airpocket-soundman/egg-analyzer/img/DSC_0775_.jpg

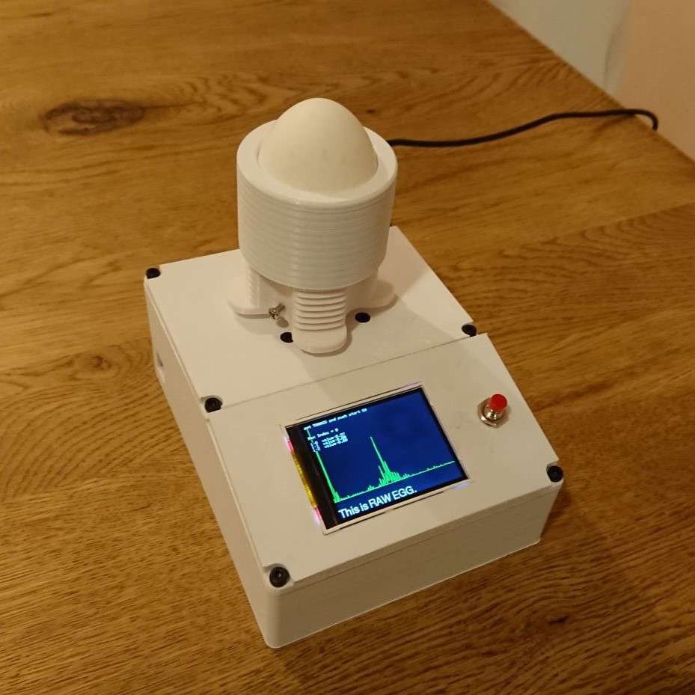
img/DSC_0775_.jpg
