airpocket-soundman/egg-analyzer/img/DSC_0773_.jpg

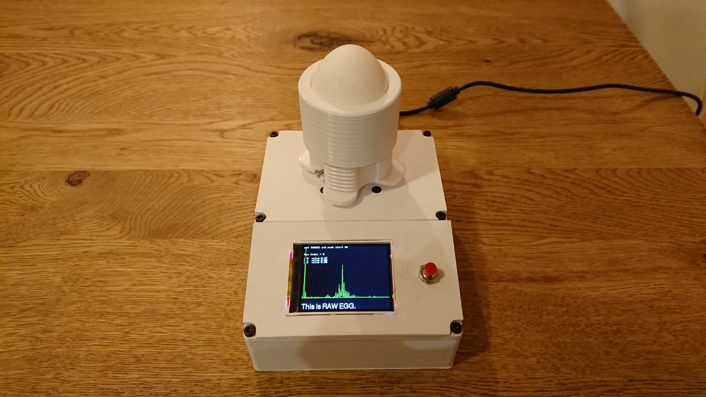
img/DSC_0773_.jpg
