airpocket-soundman/egg-analyzer/img/DSC_0776_.jpg

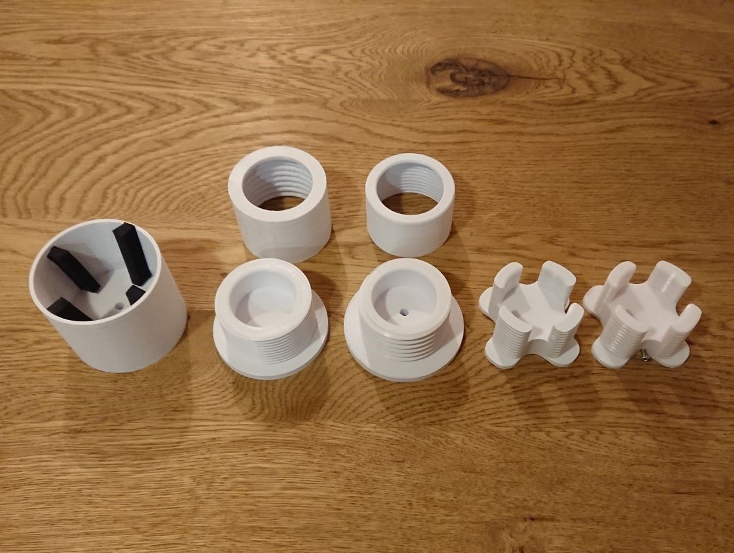
img/DSC_0776_.jpg
