airpocket-soundman/egg-analyzer/img/DSC_0781_.jpg

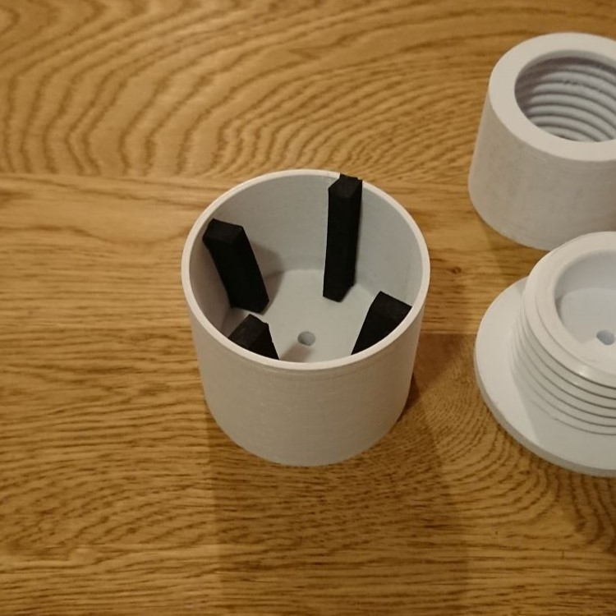
img/DSC_0781_.jpg
