airpocket-soundman/egg-analyzer/img/DSC_0782_.jpg

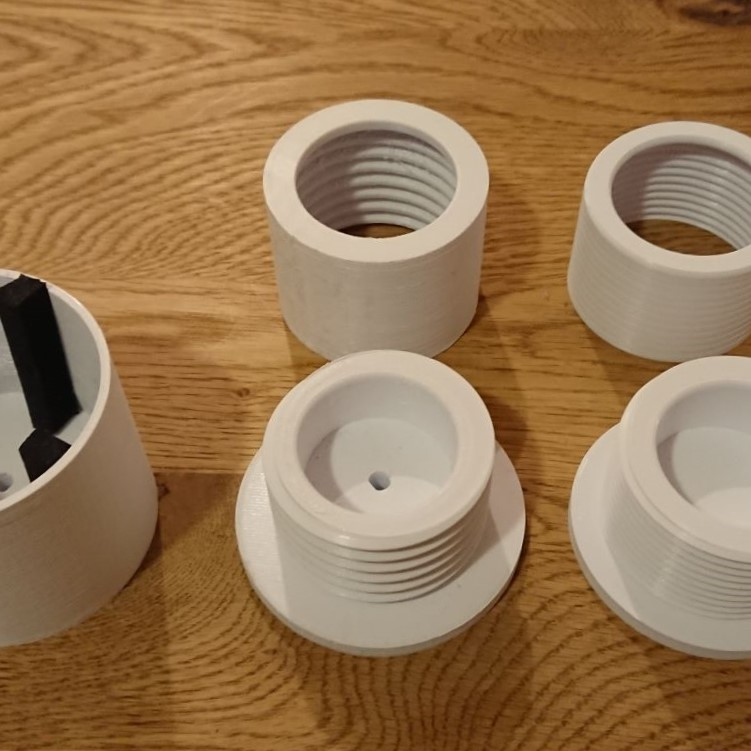
img/DSC_0782_.jpg
