airpocket-soundman/egg-analyzer/img/DSC_0783_.jpg

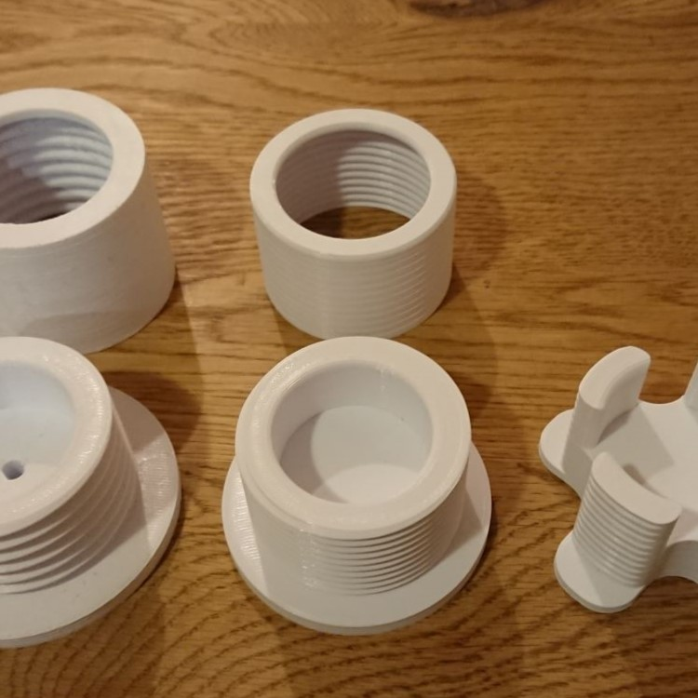
img/DSC_0783_.jpg
