airpocket-soundman/egg-analyzer/img/DSC_0785_.jpg

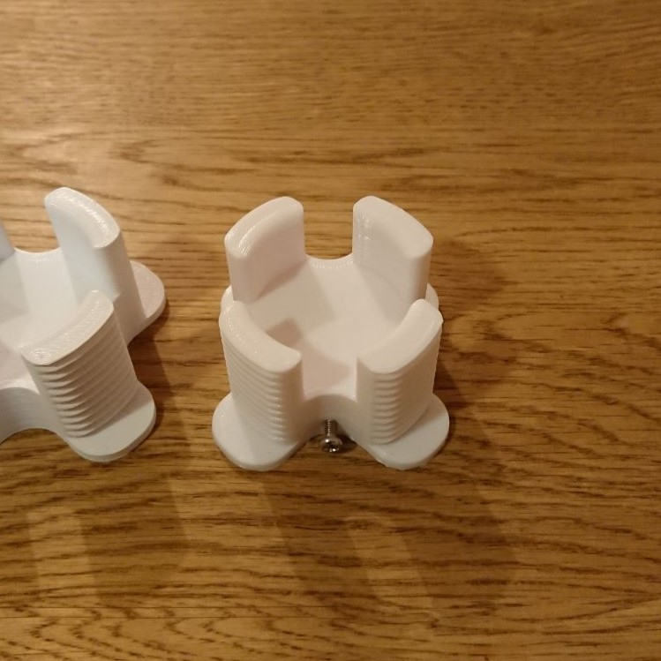
img/DSC_0785_.jpg
