airpocket-soundman/egg-analyzer/img/DSC_0789_.jpg

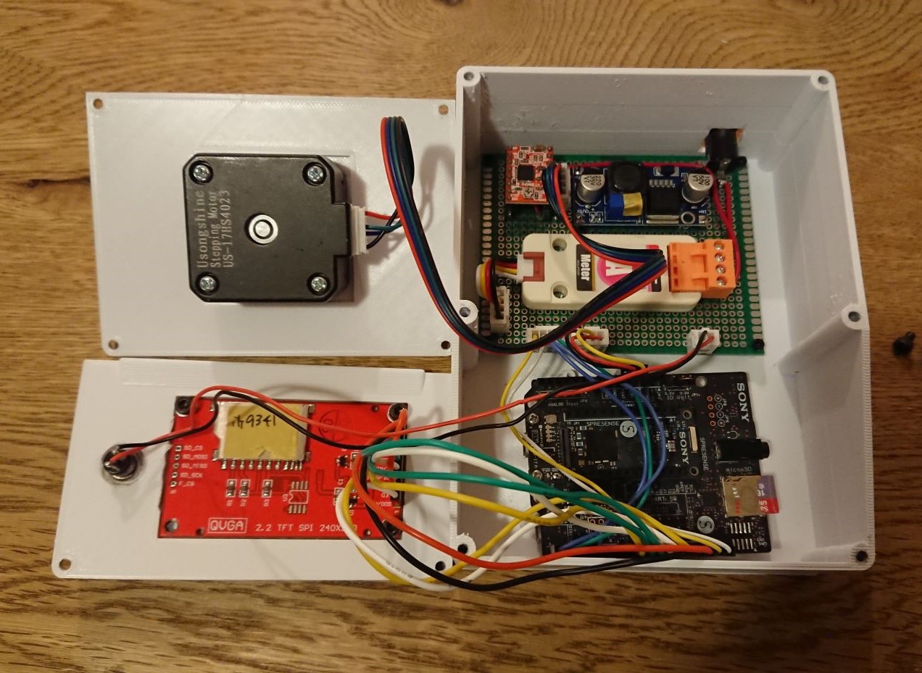
img/DSC_0789_.jpg
