airpocket-soundman/egg-analyzer/NNC/rawfiles/20240128学習用最終データ/3class_onsen.files/20240128_211705/network.png

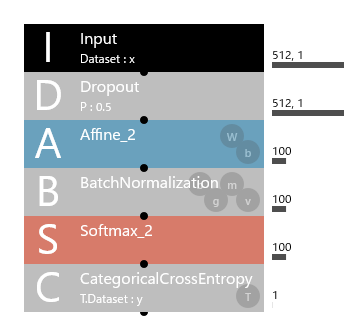
NNC/rawfiles/20240128学習用最終データ/3class_onsen.files/20240128_211705/network.png
