airpocket-soundman/egg-analyzer/NNC/rawfiles/20240128学習用最終データ/egg_data_set_test_3class_onsen.cache/cache_info.csv

x
y
