airpocket-soundman/egg-analyzer/NNC/rawfiles/20240128学習用最終データ/egg_data_set_test_3class_onsen.cache/original.csv

x:egg_data | y:state
./raw0_9x100/fft_000.csv | 0
./raw0_9x100/fft_001.csv | 0
./raw0_9x100/fft_002.csv | 0
./raw0_9x100/fft_003.csv | 0
./raw0_9x100/fft_004.csv | 0
./raw0_9x100/fft_005.csv | 0
./raw0_9x100/fft_006.csv | 0
./raw0_9x100/fft_007.csv | 0
./raw0_9x100/fft_008.csv | 0
./raw0_9x100/fft_009.csv | 0
./raw0_9x100/fft_010.csv | 0
./raw0_9x100/fft_011.csv | 0
./raw0_9x100/fft_012.csv | 0
./raw0_9x100/fft_013.csv | 0
./raw0_9x100/fft_014.csv | 0
./raw0_9x100/fft_015.csv | 0
./raw0_9x100/fft_016.csv | 0
./raw0_9x100/fft_017.csv | 0
./raw0_9x100/fft_018.csv | 0
./raw0_9x100/fft_019.csv | 0
./raw0_9x100/fft_020.csv | 0
./raw0_9x100/fft_021.csv | 0
./raw0_9x100/fft_022.csv | 0
./raw0_9x100/fft_023.csv | 0
./raw0_9x100/fft_024.csv | 0
./raw0_9x100/fft_025.csv | 0
./raw0_9x100/fft_026.csv | 0
./raw0_9x100/fft_027.csv | 0
./raw0_9x100/fft_028.csv | 0
./raw0_9x100/fft_029.csv | 0
./raw0_9x100/fft_030.csv | 0
./raw0_9x100/fft_031.csv | 0
./raw0_9x100/fft_032.csv | 0
./raw0_9x100/fft_033.csv | 0
./raw0_9x100/fft_034.csv | 0
./raw0_9x100/fft_035.csv | 0
./raw0_9x100/fft_036.csv | 0
./raw0_9x100/fft_037.csv | 0
./raw0_9x100/fft_038.csv | 0
./raw0_9x100/fft_039.csv | 0
./raw0_9x100/fft_040.csv | 0
./raw0_9x100/fft_041.csv | 0
./raw0_9x100/fft_042.csv | 0
./raw0_9x100/fft_043.csv | 0
./raw0_9x100/fft_044.csv | 0
./raw0_9x100/fft_045.csv | 0
./raw0_9x100/fft_046.csv | 0
./raw0_9x100/fft_047.csv | 0
./raw0_9x100/fft_048.csv | 0
./raw0_9x100/fft_049.csv | 0
./raw0_9x100/fft_050.csv | 0
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
./onsen10_13x100/fft_951.csv | 1
./onsen10_13x100/fft_952.csv | 1
./onsen10_13x100/fft_953.csv | 1
./onsen10_13x100/fft_954.csv | 1
./onsen10_13x100/fft_955.csv | 1
./onsen10_13x100/fft_956.csv | 1
./onsen10_13x100/fft_957.csv | 1
./onsen10_13x100/fft_958.csv | 1
./onsen10_13x100/fft_959.csv | 1
