airpocket-soundman/egg-analyzer/NNC/rawfiles/20240128学習用最終データ/3class_onsen.files/20240128_211617/network.ini

[Engine]
SDeepEngineType=NNabla
[Network_Global]
NumLayer=8
NumLink=7
[Layer_0]
ID=0
Type=Input
Position_0=24
Position_1=24
Position_2=240
Position_3=48
Property_0_Name=Name
Property_0_Value=Input
Property_1_Name=Size
Property_1_Value=512,1
Property_2_Name=Dataset
Property_2_Value=x
Property_3_Name=Generator
Property_3_Value=None
Property_4_Name=GeneratorMultiplier
Property_4_Value=1.0
Property_5_Name=Order
Property_5_Value=-1
NumProperty=6
[Layer_1]
ID=1
Type=Affine
Position_0=24
Position_1=120
Position_2=240
Position_3=48
Property_0_Name=Name
Property_0_Value=Affine
Property_1_Name=OutShape
Property_1_Value=77
Property_2_Name=WithBias
Property_2_Value=True
Property_3_Name=ParameterScope
Property_3_Value=*Name
Property_4_Name=W.File
Property_4_Value=
Property_5_Name=W.Initializer
Property_5_Value=NormalAffineGlorot
Property_6_Name=W.InitializerMultiplier
Property_6_Value=1.0
Property_7_Name=W.LRateMultiplier
Property_7_Value=1.0
Property_8_Name=b.File
Property_8_Value=
Property_9_Name=b.Initializer
Property_9_Value=Constant
Property_10_Name=b.InitializerMultiplier
Property_10_Value=0.0
Property_11_Name=b.LRateMultiplier
Property_11_Value=1.0
NumProperty=12
[Layer_2]
ID=2
Type=Softmax
Position_0=24
Position_1=168
Position_2=240
Position_3=48
Property_0_Name=Name
Property_0_Value=Softmax
Property_1_Name=Axis
Property_1_Value=0
NumProperty=2
[Layer_3]
ID=3
Type=Softmax
Position_0=24
Position_1=312
Position_2=240
Position_3=48
Property_0_Name=Name
Property_0_Value=Softmax_2
Property_1_Name=Axis
Property_1_Value=0
NumProperty=2
[Layer_4]
ID=4
Type=Affine
Position_0=24
Position_1=216
Position_2=240
Position_3=48
Property_0_Name=Name
Property_0_Value=Affine_2
Property_1_Name=OutShape
Property_1_Value=100
Property_2_Name=WithBias
Property_2_Value=True
Property_3_Name=ParameterScope
Property_3_Value=*Name
Property_4_Name=W.File
Property_4_Value=
Property_5_Name=W.Initializer
Property_5_Value=NormalAffineGlorot
Property_6_Name=W.InitializerMultiplier
Property_6_Value=1.0
Property_7_Name=W.LRateMultiplier
Property_7_Value=1.0
Property_8_Name=b.File
Property_8_Value=
Property_9_Name=b.Initializer
Property_9_Value=Constant
Property_10_Name=b.InitializerMultiplier
Property_10_Value=0.0
Property_11_Name=b.LRateMultiplier
Property_11_Value=1.0
NumProperty=12
[Layer_5]
ID=5
Type=CategoricalCrossEntropy
Position_0=24
Position_1=360
Position_2=240
Position_3=48
Property_0_Name=Name
Property_0_Value=CategoricalCrossEntropy
Property_1_Name=Axis
Property_1_Value=0
Property_2_Name=T.Dataset
Property_2_Value=y
Property_3_Name=T.Generator
Property_3_Value=None
Property_4_Name=T.GeneratorMultiplier
Property_4_Value=1.0
NumProperty=5
[Layer_6]
ID=6
Type=BatchNormalization
Position_0=24
Position_1=264
Position_2=240
Position_3=48
Property_0_Name=Name
Property_0_Value=BatchNormalization
Property_1_Name=Axes
Property_1_Value=0
Property_2_Name=DecayRate
Property_2_Value=0.9
Property_3_Name=Epsilon
Property_3_Value=0.0001
Property_4_Name=BatchStat
Property_4_Value=True
Property_5_Name=ParameterScope
Property_5_Value=*Name
Property_6_Name=beta.File
Property_6_Value=
Property_7_Name=beta.Initializer
Property_7_Value=Constant
Property_8_Name=beta.InitializerMultiplier
Property_8_Value=0.0
Property_9_Name=beta.LRateMultiplier
Property_9_Value=1.0
Property_10_Name=gamma.File
Property_10_Value=
Property_11_Name=gamma.Initializer
Property_11_Value=Constant
Property_12_Name=gamma.InitializerMultiplier
Property_12_Value=1.0
Property_13_Name=gamma.LRateMultiplier
Property_13_Value=1.0
Property_14_Name=mean.File
Property_14_Value=
Property_15_Name=mean.Initializer
Property_15_Value=Constant
Property_16_Name=mean.InitializerMultiplier
Property_16_Value=0.0
Property_17_Name=mean.LRateMultiplier
Property_17_Value=0.0
Property_18_Name=var.File
Property_18_Value=
Property_19_Name=var.Initializer
Property_19_Value=Constant
Property_20_Name=var.InitializerMultiplier
Property_20_Value=0.0
Property_21_Name=var.LRateMultiplier
Property_21_Value=0.0
NumProperty=22
[Layer_7]
ID=7
Type=Tanh
Position_0=24
Position_1=72
Position_2=240
Position_3=48
Property_0_Name=Name
Property_0_Value=Tanh
NumProperty=1
[Link_0]
ID=1
SourceLayerID=1
SourcePinIndex=0
DestLayerID=2
DestPinIndex=0
[Link_1]
ID=2
SourceLayerID=2
SourcePinIndex=0
DestLayerID=4
DestPinIndex=0
[Link_2]
ID=4
SourceLayerID=3
SourcePinIndex=0
DestLayerID=5
DestPinIndex=0
[Link_3]
ID=5
SourceLayerID=4
SourcePinIndex=0
DestLayerID=6
DestPinIndex=0
[Link_4]
ID=6
SourceLayerID=6
SourcePinIndex=0
DestLayerID=3
DestPinIndex=0
[Link_5]
ID=7
SourceLayerID=0
SourcePinIndex=0
DestLayerID=7
DestPinIndex=0
[Link_6]
ID=8
SourceLayerID=7
SourcePinIndex=0
DestLayerID=1
DestPinIndex=0
[Dataset]
Num=2
MainIndex=0
[Dataset_0]
Name=Training
URI=C:\Users\yamas\Desktop\20240128\egg_data_set_test_3class_onsen.csv
Shuffle=1
EnableCache=0
ImageNormalization=1
NumData=1800
[Dataset_1]
Name=Validation
URI=C:\Users\yamas\Desktop\20240128\egg_data_set_valid_3class_onsen.csv
Shuffle=0
EnableCache=0
ImageNormalization=1
NumData=1200
[Description]
Text=
[Config]
MaxEpoch=100
SaveBest=1
BatchSize=64
TypeConfig=Float
MonitorInterval=10
AutoEvaluation=0
NumOptimizer=1
NumMonitor=2
NumExecutor=1
[Optimizer_0]
RangeFrom=-1
RangeTo=-1
RangeUnit=0
Optimizer_Name=Optimizer
Optimizer_NetworkName=Main
Optimizer_DatasetName=Training
UpdateInterval=1
SolverName=Adam
SolverParameterNum=4
SolverParameterName_0=Alpha
SolverParameter_0=0.001
SolverParameterName_1=Beta1
SolverParameter_1=0.9
SolverParameterName_2=Beta2
SolverParameter_2=0.999
SolverParameterName_3=Epsilon
SolverParameter_3=1e-08
WeightDecay=0
LearningRateScheduler=Exponential
LearningRateMultiplier=1
LearningRateUpdateInterval=1
LearningRateUpdateIntervalUnit=0
LearningRatePower=1
LearningRateSteps=
LearningRateWarmupScheduler=None
LearningRateWarmupLength=0
LearningRateWarmupLengthUnit=0
[Monitor_0]
Monitor_Name=train_error
Monitor_NetworkName=MainValidation
Monitor_DatasetName=Training
[Monitor_1]
Monitor_Name=valid_error
Monitor_NetworkName=MainValidation
Monitor_DatasetName=Validation
[Executor_0]
Executor_Name=Executor
Executor_NetworkName=MainRuntime
Executor_DatasetName=Validation
NumEvaluations=1
RepeatEvaluationType=0
NeedBackPropagation=0
[StructureSearch]
Enabled=1
Method=Random
Objective=ErrorAndCalculation
Validation_Min=-1
Validation_Max=-1
CostMultiplyAdd_Min=-1
CostMultiplyAdd_Max=-1
EarlyStopping=0
TimeLimit=0
[OutOfCoreTraining]
Enabled=0
GPUMemorySize=0
WindowSize=0
[Temporary]
CommandType=Normal
TrainingPluginName=
TrainingPluginFileName=
TrainingPluginArgs=
